generator-control/genfield/Ourtasks/GenfieldTask.h

/******************************************************************************
* File Name          : GenfieldTask.h
* Date First Issued  : 01/06/2020
* Description        : Genfield function w STM32CubeMX w FreeRTOS
*******************************************************************************/

#ifndef __GENFIELDTASK
#define __GENFIELDTASK

#include <stdint.h>
#include "FreeRTOS.h"
#include "task.h"
#include "cmsis_os.h"
#include "stm32f1xx_hal.h"
#include "adc_idx_v_struct.h"
#include "CanTask.h"

/* 
=========================================      
CAN msgs: 
ID suffix: "_i" = incoming msg; "_r" response msg

RECEIVED msgs directed into genfield function:
 (1) genfield command (also keep-alive) "cid_keepalive_i"
     payload[0]
       bit 7 - connect request
       bit 6 - reset critical error
 (2) poll (time sync) "cid_gps_sync"
 (3) function command (diagnostic poll) "cid_cmd_i"
    
SENT by genfield function:
 (1) genfield command "cid_keepalive_r" (response to "cid_keepalive_i")
     payload[0]
       bit 7 - faulted (code in payload[2])
       bit 6 - warning: minimum pre-chg immediate connect.
              (warning bit only resets with power cycle)
		 bit[0]-[3]: Current main state code

     payload[1] = critical error state error code
         0 = No fault
         1 = battery string voltage (hv1) too low
         2 = genfield 1 de-energized, aux1 closed
         3 = genfield 2 de-energized, aux2 closed
         4 = genfield #1 energized, after closure delay aux1 open
         5 = genfield #2 energized, after closure delay aux2 open
         6 = genfield #1 does not appear closed
         7 = Timeout before pre-charge voltage reached cutoff
         8 = Genfield #1 closed but voltage across it too big
         9 = Genfield #2 closed but voltage across it too big

		payload[2]
         bit[0]-[3] - current substate CONNECTING code
         bit[4]-[7] - current substate (spare) code

 poll  (response to "cid_gps_sync") & heartbeat
 (2)  "cid_msg1" hv #1 : current #1  battery string voltage:current
 (3)	"cid_msg2" hv #2 : hv #3       DMOC+:DMOC- voltages

 function command "cid_cmd_r"(response to "cid_cmd_i")
 (4)  conditional on payload[0], for example(!)--
      - ADC ct for calibration purposes hv1
      - ADC ct for calibration purposes hv2
      - ADC ct for calibration purposes hv3
      - ADC ct for calibration purposes current1
      - ADC ct for calibration purposes current2
      - Duration: (Energize coil 1 - aux 1)
      - Duration: (Energize coil 2 - aux 2)
      - Duration: (Drop coil 1 - aux 1)
      - Duration: (Drop coil 2 - aux 2)
      - volts: 12v CAN supply
      - volts: 5v regulated supply
      ... (many and sundry)

 heartbeat (sent in absence of keep-alive msgs)
 (5)  "cid_hb1" Same as (2) above
 (6)  "cid_hb2" Same as (3) above

=========================================    
NOTES:
1. GENFIELD DESIGNATION--
   (Important for following GenfieldStates.c code)

   a. Two genfield configuration
      #1 Battery string plus-to-DMOC plus
      #2 Battery string minus-to-DMOC minus
          with pre-charge resistor across #2's contacts.

   b. One genfield (with small pre-charge relay)
      #1 Battery string plus-to-DMOC plus
      #2 Battery string plus-to-pre-charge resistor,
          with pre-charge resistor to DMOC plus

2. The command/keep-alive msgs are sent
   - As a response to every command/keep-alive
   - Immediately when the program state changes
   - Every keep-alive timer timeout when incoming keep-alive
     msgs are not being receive, i.e. becomes a status heartbeat.

3. hv3 cannot measure negative voltages which might occur during
   regeneration with genfield #2 closed.  Likewise, hv2 can 
   exceed hv1 so that the difference becomes negative.  In both
   case the negative values would be small.

*/


/* Task notification bit assignments. */
#define CNCTBIT00	(1 << 0)  // ADCTask has new readings
#define CNCTBIT01	(1 << 1)  // HV sensors usart RX line ready
#define CNCTBIT02	(1 << 2)  // spare
#define CNCTBIT03	(1 << 3)  // TIMER 3: uart RX keep-alive
#define CNCTBIT04	(1 << 4)  // TIMER 1: Command Keep Alive
#define CNCTBIT05	(1 << 5)  // TIMER 2: Multiple use delays
// MailboxTask notification bits for CAN msg mailboxes
#define CNCTBIT06	(1 << 6)  // CANID_CMD: incoming command:        cid_cmd_i 
#define CNCTBIT07	(1 << 7)  // CANID-keepalive connect command:    cid_keepalive_i
#define CNCTBIT08	(1 << 8)  // CANID-GPS time sync msg (poll msg): cid_gps_sync

/* Event status bit assignments (CoNtaCTor EVent ....) */
#define CNCTEVTIMER1 (1 << 0) // 1 = timer1 timed out: command/keep-alive
#define CNCTEVTIMER2 (1 << 1) // 1 = timer2 timed out: delay
#define CNCTEVTIMER3 (1 << 2) // 1 = timer3 timed out: uart RX/keep-alive
#define CNCTEVCACMD  (1 << 3) // 1 = CAN rcv: general purpose command
#define CNCTEVCANKA  (1 << 4) // 1 = CAN rcv: Keep-alive/command
#define CNCTEVCAPOL  (1 << 5) // 1 = CAN rcv: Poll
#define CNCTEVCMDRS  (1 << 6) // 1 = Command to reset
#define CNCTEVCMDCN  (1 << 7) // 1 = Command to connect
#define CNCTEVHV     (1 << 8) // 1 = New HV readings
#define CNCTEVADC    (1 << 9) // 1 = New ADC readings

/* Output status bit assignments */
#define CNCTOUT00K1  (1 << 0) // 1 = genfield #1 energized
#define CNCTOUT01K2  (1 << 1) // 1 = genfield #2 energized
#define CNCTOUT02X1  (1 << 2) // 1 = aux #1 closed
#define CNCTOUT03X2  (1 << 3) // 1 = aux #2 closed
#define CNCTOUT04EN  (1 << 4) // 1 = DMOC enable FET
#define CNCTOUT05KA  (1 << 5) // 1 = CAN msg queue: KA status
#define CNCTOUT06KAw (1 << 6) // 1 = genfield #1 energized & pwm'ed
#define CNCTOUT07KAw (1 << 7) // 1 = genfield #2 energized & pwm'ed
#define CNCTOUTUART3 (1 << 8) // 1 = uart3 rx with high voltage timer timed out

/* AUX contact pins. */
#define AUX1_GPIO_REG GPIOA
#define AUX1_GPIO_IN  GPIO_PIN_1
#define AUX2_GPIO_REG GPIOA
#define AUX2_GPIO_IN  GPIO_PIN_5

/* HV by-pass jumper pin. */
#define HVBYPASSPINPORT GPIOA
#define HVBYPASSPINPIN  GPIO_PIN_3

/* Command request bits assignments. */
#define CMDCONNECT (1 << 7) // 1 = Connect requested; 0 = Disconnect requested
#define CMDRESET   (1 << 6) // 1 = Reset fault requested; 0 = no command

/* Number of different CAN id msgs this function sends. */
# define NUMCANMSGS 6

/* High voltage readings */
//#define HVSCALEbits 16  // Scale factor HV

struct CNCNTHV
{
	struct IIRFILTERL iir; // Intermediate filter params
//   double dhv;            // Calibrated
	double dscale;         // volts/tick
	double dhvc;           // HV calibrated
	uint32_t hvcal;        // Calibrated, scaled volts/adc tick
	uint32_t hvc;          // HV as scaled volts
	uint16_t hv;           // Raw ADC reading as received from uart

};

/* Fault codes */
enum GENFIELD_FAULTCODE
{
	NOFAULT,
	BATTERYLOW,
	GENFIELD1_OFF_AUX1_ON,
	GENFIELD2_OFF_AUX2_ON,
	GENFIELD1_ON_AUX1_OFF,
	GENFIELD2_ON_AUX2_OFF,
	GENFIELD1_DOES_NOT_APPEAR_CLOSED,
   PRECHGVOLT_NOTREACHED,
	GENFIELD1_CLOSED_VOLTSTOOBIG,
	GENFIELD2_CLOSED_VOLTSTOOBIG,
	KEEP_ALIVE_TIMER_TIMEOUT,
	NO_UART3_HV_READINGS,
	HE_AUTO_ZERO_TOLERANCE_ERR,
};

enum GENFIELD_STATE
{
	DISCONNECTED,   /*  0 */
	CONNECTING,     /*  1 */
	CONNECTED,      /*  2 */
	FAULTING,       /*  3 */
	FAULTED,        /*  4 */
	RESETTING,      /*  5 */
	DISCONNECTING,  /*  6 */
	OTOSETTLING,    /*  7 one time intializing. */
};

/* Function command response payload codes. */
enum GENFIELD_CMD_CODES
{
	ADCRAW5V,         // PA0 IN0  - 5V sensor supply
	ADCRAWCUR1,       // PA5 IN5  - Current sensor: total battery current
	ADCRAWCUR2,       // PA6 IN6  - Current sensor: motor
	ADCRAW12V,        // PA7 IN7  - +12 Raw power to board
	ADCINTERNALTEMP,  // IN17     - Internal temperature sensor
	ADCINTERNALVREF,  // IN18     - Internal voltage reference
	UARTWHV1,
	UARTWHV2,
	UARTWHV3,
	CAL5V,
	CAL12V,
};

/* CAN msg array index names. */
enum CANCMD_R
{
CID_KA_R,
CID_MSG1,
CID_MSG2,
CID_CMD_R,
CID_HB1,
CID_HB2,
};

/* Working struct for Genfield function/task. */
// Prefixes: i = scaled integer, f = float
// Suffixes: k = timer ticks, t = milliseconds
struct GENFIELDFUNCTION
{
   // Parameter loaded either by high-flash copy, or hard-coded subroutine
	struct GENFIELDLC lc; // Parameters for genfields, (lc = Local Copy)

	struct ADCFUNCTION* padc; // Pointer to ADC working struct

	/* Events status */
	uint32_t evstat;

	/* Output status */
	uint32_t outstat;
	uint32_t outstat_prev;

	/* Current fault code */
	enum GENFIELD_FAULTCODE faultcode;
	enum GENFIELD_FAULTCODE faultcode_prev;

	/* OTO settling */
	uint32_t otosw;

/* In the disconnect state the battery string voltage must be above the following. */
	uint32_t ibattlow;   // Minimum battery volts required to connect

/* Battery string current above which disconnecting is prevented. */
	int32_t icurrentdisconnect; // Scale integer representation

/* With two genfield config, (hv1-hv2) max when genfield #1 closes */
/* In one genfield config, (hv1-hv2) max when genfield #2 closes */
	uint32_t ihv1mhv2max;

	uint32_t iprechgendv;  // Prep-charge end volts threshold: two genfield mode
	uint32_t iprechgendvb; // Prep-charge end volts threshold: one genfield mode (b)


/* Mininum pre-charge delay (before monitoring voltage) */
   uint32_t prechgmin_k; // Minimum pre-charge duration

	uint32_t idiffafter; //  Scaled int of lc.diffafter

	uint32_t ka_k;       // Command/Keep-alive CAN msg timeout duration.
	uint32_t prechgmax_k;// allowable delay for diffafter to reach closure point (timeout delay ticks)
	uint32_t close1_k;   // genfield #1 coil energize-closure (timeout delay ticks)
	uint32_t close2_k;   // genfield #2 coil energize-closure (timeout delay ticks)
	uint32_t open1_k;    // genfield #1 coil de-energize-open (timeout delay ticks)
	uint32_t open2_k;    // genfield #2 coil de-energize-open (timeout delay ticks)
	uint32_t keepalive_k;// keep-alive timeout (timeout delay ticks)
	uint32_t hbct1_k;		// Heartbeat ct: ticks between sending msgs hv1:cur1
	uint32_t hbct2_k;		// Heartbeat ct: ticks between sending msgs hv2:cur2

	uint32_t ihv1;       // Latest reading: battery string at genfield #1
	uint32_t ihv2;       // Latest reading: DMOC side of genfield #1
	uint32_t ihv3;       // Latest reading: Pre-charge R, (if two genfield config)
	int32_t hv1mhv2;     // Voltage across genfield #1 from latest readings

	uint32_t statusbits;
	uint32_t statusbits_prev;

	/* Setup serial receive for uart (HV sensing) */
	struct SERIALRCVBCB* prbcb3;	// usart3

	TimerHandle_t swtimer1; // Software timer1: command/keep-alive
	TimerHandle_t swtimer2; // Software timer2: multiple purpose delay
	TimerHandle_t swtimer3; // Software timer3: uart RX/keep-alive

	/* High voltage readings */
	struct CNCNTHV hv[NUMHV];
	uint32_t hvuartctr;	// Running count of uart lines received from hv sensor

	/* Pointers to incoming CAN msg mailboxes. */
	struct MAILBOXCAN* pmbx_cid_cmd_i;      //
	struct MAILBOXCAN* pmbx_cid_keepalive_i; //
	struct MAILBOXCAN* pmbx_cid_gps_sync;   //

	uint32_t ipwmpct1;     // Period ct PWM after closure delay at 100% coil #1
	uint32_t ipwmpct2;     // Period ct PWM after closure delay at 100% coil #2

	/* PWM struct */
	TIM_OC_InitTypeDef sConfigOCn; // 'n' - serves ch3 and ch4
	
	uint8_t state;      // Genfield main state
	uint8_t substateC;  // State within CONNECTING (0-15)
	uint8_t substateX;  // spare substate (0-15)

	/* CAN msgs */
	struct CANTXQMSG canmsg[NUMCANMSGS];
};

/* *************************************************************************/
osThreadId xGenfieldTaskCreate(uint32_t taskpriority);
/* @brief	: Create task; task handle created is global for all to enjoy!
 * @param	: taskpriority = Task priority (just as it says!)
 * @return	: GenfieldTaskHandle
 * *************************************************************************/
void StartGenfieldTask(void const * argument);
/*	@brief	: Task startup
 * *************************************************************************/

extern struct GENFIELDFUNCTION genfieldfunction;
extern osThreadId GenfieldTaskHandle;

#endif
