generator-control/genfield/Ourtasks/genfield_idx_v_struct.h

/******************************************************************************
* File Name          : genfield_idx_v_struct.h
* Date First Issued  : 06/26/2019
* Board              :
* Description        : Load parameter struct
*******************************************************************************/

#include <stdint.h>
#include "common_can.h"
#include "iir_filter_lx.h"
#include "GenfieldTask.h"

#ifndef __GENFIELD_IDX_V_STRUCT
#define __GENFIELD_IDX_V_STRUCT

/* Hardware configuration option bit assignments. */
#define AUX1PRESENT   (1 << 0)  // 1 = Genfield #1 has auxilary contacts
#define AUX1SENSE     (1 << 1)  // 1 = Aux I/O bit with Genfield #1 closed
#define AUX2PRESENT   (1 << 2)  // 1 = Genfield #2 has auxilary contacts
#define AUX2SENSE     (1 << 3)  // 1 = Aux I/O bit with Genfield #2 closed
#define ONEGENFIELD  (1 << 4)  // 1 = One genfield; one small pre-charge relay
#define PWMGENFIELD1 (1 << 5)  // 1 = PWM'ing is used on coil #1
#define PWMGENFIELD2 (1 << 6)  // 1 = PWM'ing is used on coil #2
#define PWMNOHVSENSOR (1 << 7)  // 1 = No high voltage sensor, (ignore hv readings)

/* High Voltage readings arrive in on uart line. */
#define NUMHV 3       // Number of hv readings
#define	IDXHV1  0 // High voltage reading: battery string side of genfield
#define	IDXHV2  1 // High voltage reading: DMOC+ side of genfield
#define	IDXHV3  2 // High voltage reading: across pre-charge resistor (two genfields)

#define HVSCALE (1 << 17) // High voltage integer scaling for hvcal


/* Calibration parameter, float */
// Use double for F103 to save float->double conversions
struct CNTCTCALHV
{
	struct IIR_L_PARAM iir; // Filter: Time constant, integer scaling
	double dvcal;       // Calibration voltage applied
	uint32_t adchv;     // ADC reading for calibration voltage
	uint32_t offset;    // ADC reading for Sensor zero
};
struct CNTCTCALF
{
	double offset;
	double scale;
};
/* Calibration parameters, scaled integer */
struct CNTCTCALSI
{
	int32_t offset;
	int32_t scale;
};

/* Parameters genfield instance */
struct GENFIELDLC
 {
	uint32_t size;			// Number of items in struct
 	uint32_t crc;			// crc-32 placed by loader
	uint32_t version;		// struct version number
	double ddiffb4;      // hv1-hv2 voltage difference before closing (volts)

/* NOTE: 
   - all suffix _t parameters are times in milliseconds
   - all voltages are in volts; prefix 'f' designates float */
	
/* Hardware configuration option bits. */
   uint32_t hwconfig;

/* Command/Keep-alive CAN msg timeout duration. */
	uint32_t ka_t;       // (e.g. 1000 ms)

/* uart RX keep-alive timeout duration. */
   uint32_t ksRX_t;     // (e.g. 10 ms)

/* In the disconnect state the battery string voltage must be above the following. */
	float fbattlow;      // Minimum battery volts required to connect

/* Battery string current above which disconnecting is prevented. */
	double dcurrentdisconnect;   // Parameter specification made in fp

/* Genfield #1 closure time delay */
	uint32_t close1_t;   // Delay: genfield #1 coil energize->closed

/* Genfield #2, or pre-charge relay, closure time delay */
	uint32_t close2_t;   // Delay: #2 coil energize->closed
   
/* Genfield #1 open time delay */
	uint32_t open1_t;   // Delay: genfield #1 coil de-energize->open

/* Genfield #2, or pre-charge relay, open time delay */
	uint32_t open2_t;   // Delay: #2 coil de-energize->open

/* Mininum pre-charge delay (before monitoring voltage) */
   uint32_t prechgmin_t; // Minimum pre-charge duration

/* Maximum pre-charge wait, after prechgmin_t, for voltage threshold
   to be reached. */
   uint32_t prechgmax_t; // Maximum allowed for voltage to reach threshold

/* Allowable hv1-hv2 voltage difference after closure (volts) */
	float fdiffafter;

/* HV2 reading stable after closure (duration ms) */
	uint32_t hv2stable_t;

/* PWM durations (0.0- 100.0) */
   float  fpwmpct1;     // Percent PWM after closure delay at 100% coil #1
   float  fpwmpct2;     // Percent PWM after closure delay at 100% coil #2

/* Message timings. */
	uint32_t keepalive_t;// keep-alive timeout (timeout delay ms)
	uint32_t hbct1_t;		// Heartbeat ct: ticks between sending msgs hv1:cur1
	uint32_t hbct2_t;		// Heartbeat ct: ticks between sending msgs hv2:cur2
	uint32_t hbct3_t;		// Heartbeat ct: ticks between sending msgs hv3 (if two genfields)

/* Calibrations (offset, scale) */

	// High voltage from uart
	struct CNTCTCALHV calhv[NUMHV]; 

/* Send CAN ids  */
	uint32_t cid_hb1;    // CANID-Heartbeat msg volt1:cur1 (volts:amps)
	uint32_t cid_hb2;    // CANID-Heartbeat msg volt2:cur2 (volts:amps)
   uint32_t cid_msg1;   // CANID-genfield poll response msg: volt1:cur1 (volts:amps)
   uint32_t cid_msg2;   // CANID-genfield poll response msg: volt2:cur2 (volts:amps)
	uint32_t cid_cmd_r;  // CANID_CMD_CNTCTR1R
	uint32_t cid_keepalive_r; // CANID-keepalive response (status)

/* Receive CAN ids List of CAN ID's for setting up hw filter */
	uint32_t cid_cmd_i;       // CANID_CMD: incoming command
	uint32_t cid_keepalive_i;// CANID-keepalive connect command
	uint32_t cid_gps_sync;    // CANID-GPS time sync msg (poll msg)
	uint32_t code_CAN_filt[5];// Spare
 };

/* *************************************************************************/
void genfield_idx_v_struct_hardcode_params(struct GENFIELDLC* p);
/* @brief	: Init struct from hard-coded parameters (rather than database params in highflash)
 * @return	: 0
 * *************************************************************************/
 
#endif
