generator-control/genfield/Ourwares/ADCTask.c

/******************************************************************************
* File Name          : ADCTask.c
* Date First Issued  : 02/01/2019
* Description        : Processing ADC readings after ADC/DMA issues interrupt
*******************************************************************************/

#include "FreeRTOS.h"
#include "task.h"
#include "cmsis_os.h"
#include "malloc.h"

#include "ADCTask.h"
#include "adctask.h"
#include "morse.h"
#include "adcfastsum16.h"
#include "adcparams.h"
#include "GenfieldTask.h"
#include "adcextendsum.h"

void StartADCTask(void const * argument);

uint32_t adcsumdb[6]; // debug
uint32_t adcdbctr = 0;// debug

osThreadId ADCTaskHandle;

extern ADC_HandleTypeDef hadc1;

extern osThreadId GenfieldTaskHandle;

/* *************************************************************************
 * osThreadId xADCTaskCreate(uint32_t taskpriority);
 * @brief	: Create task; task handle created is global for all to enjoy!
 * @param	: taskpriority = Task priority (just as it says!)
 * @return	: ADCTaskHandle
 * *************************************************************************/
osThreadId xADCTaskCreate(uint32_t taskpriority)
{
 	osThreadDef(ADCTask, StartADCTask, osPriorityNormal, 0, 128);
	ADCTaskHandle = osThreadCreate(osThread(ADCTask), NULL);
	vTaskPrioritySet( ADCTaskHandle, taskpriority );
	return ADCTaskHandle;

}
/* *************************************************************************
 * void StartADCTask(void const * argument);
 *	@brief	: Task startup
 * *************************************************************************/
void StartADCTask(void const * argument)
{
	#define TSK02BIT02	(1 << 0)  // Task notification bit for ADC dma 1st 1/2 (adctask.c)
	#define TSK02BIT03	(1 << 1)  // Task notification bit for ADC dma end (adctask.c)

	uint16_t* pdma;

	/* A notification copies the internal notification word to this. */
	uint32_t noteval = 0;    // Receives notification word upon an API notify

	/* notification bits processed after a 'Wait. */
	uint32_t noteused = 0;

	/* Get buffers, "our" control block, and ==>START<== ADC/DMA running. */
	struct ADCDMATSKBLK* pblk = adctask_init(&hadc1,TSK02BIT02,TSK02BIT03,&noteval);
	if (pblk == NULL) {morse_trap(15);}

  /* Infinite loop */
  for(;;)
  {
		/* Wait for DMA interrupt notification from adctask.c */
		xTaskNotifyWait(noteused, 0, &noteval, portMAX_DELAY);
		noteused = 0;	// Accumulate bits in 'noteval' processed.

		/* We handled one, or both, noteval bits */
		noteused |= (pblk->notebit1 | pblk->notebit2);

		if (noteval & TSK02BIT02)
		{
			pdma = adc1dmatskblk[0].pdma1; // [0] = adc1
		}
		else
		{
			pdma = adc1dmatskblk[0].pdma2;
		}

		/* Sum the readings 1/2 of DMA buffer to an array. */
		adcfastsum16(&adc1.chan[0], pdma); // Fast in-line addition
		adc1.ctr += 1; // Update count

#define DEBUGGINGADCREADINGS
#ifdef DEBUGGINGADCREADINGS
		/* Save sum for defaultTask printout for debugging */
		adcsumdb[0] = adc1.chan[0].sum;
		adcsumdb[1] = adc1.chan[1].sum;
		adcsumdb[2] = adc1.chan[2].sum;
		adcsumdb[3] = adc1.chan[3].sum;
		adcsumdb[4] = adc1.chan[4].sum;
		adcsumdb[5] = adc1.chan[5].sum;
		adcdbctr += 1;
#endif

		/* Extended sum for smoothing and display. */
		adcextendsum(&adc1);

		/* Calibrate and filter ADC readings. */
		adcparams_cal();

		/* Notify GenfieldTask that new readings are ready. */
		if( GenfieldTaskHandle == NULL) morse_trap(51); // JIC task has not been created
		
		xTaskNotify(GenfieldTaskHandle, CNCTBIT00, eSetBits);
  }
}
