generator-control/genfield/Ourwares/CanTask.c

/******************************************************************************
* File Name          : CanTask.c
* Date First Issued  : 01/01/2019
* Description        : CAN interface to FreeRTOS/ST HAL
*******************************************************************************/

#include "stm32f1xx_hal.h"
#include "stm32f1xx_hal_can.h"
#include "CanTask.h"
#include "can_iface.h"
#include "morse.h"

void StartCanTxTask(void const * argument);
void StartCanRxTask(void const * argument);

osThreadId CanTxTaskHandle;
QueueHandle_t CanTxQHandle;

/* ====== Tx ==============================================================*/
/* *************************************************************************
 * void canmsg_expand(CAN_TxHeaderTypeDef *phal, uint8_t *pdat, struct CANRCVBUF *pcan);
 * @brief	: Convert hardware compressed format to silly HAL expanded format
 * @param	: phal = pointer to HAL output
 * @param	: pdat = pointer to HAL payload data array
 * @param	: pcan = pointer to convenient hardware format
 * *************************************************************************/
void canmsg_expand(CAN_TxHeaderTypeDef *phal, uint8_t *pdat, struct CANRCVBUF *pcan)
{
	phal->StdId = (pcan->id >> 21);
	phal->ExtId = (pcan->id >>  3);
	phal->IDE   = (pcan->id & CAN_ID_EXT);
	phal->RTR   = (pcan->id & CAN_RTR_REMOTE);
	phal->DLC   = (pcan->dlc & 0x7);
	*(pdat+0) = pcan->cd.uc[0];
	*(pdat+1) = pcan->cd.uc[1];
	*(pdat+2) = pcan->cd.uc[2];
	*(pdat+3) = pcan->cd.uc[3];
	*(pdat+4) = pcan->cd.uc[4];
	*(pdat+5) = pcan->cd.uc[5];
	*(pdat+6) = pcan->cd.uc[6];
	*(pdat+7) = pcan->cd.uc[7];
	return;
}

/* *************************************************************************
 * QueueHandle_t  xCanTxTaskCreate(uint32_t taskpriority, int32_t queuesize);
 * @brief	: Create task; task handle created is global for all to enjoy!
 * @param	: taskpriority = Task priority (just as it says!)
 * @param	: queuesize = number of items in Tx queue
 * @return	: QueueHandle_t = queue handle
 * *************************************************************************/
QueueHandle_t  xCanTxTaskCreate(uint32_t taskpriority, int32_t queuesize)
{
 /* definition and creation of CanTask */
  osThreadDef(CanTxTask, StartCanTxTask, osPriorityNormal, 0, 128);
  CanTxTaskHandle = osThreadCreate(osThread(CanTxTask), NULL);
	vTaskPrioritySet( CanTxTaskHandle, taskpriority );

	/* FreeRTOS queue for task with data to send. */
	CanTxQHandle = xQueueCreate(queuesize, sizeof(struct CANTXQMSG));
	return CanTxQHandle;
}
/* *************************************************************************
 * void StartCanTxTask(void const * argument);
 *	@brief	: Task startup
 * *************************************************************************/
void StartCanTxTask(void const * argument)
{
   BaseType_t Qret;	// queue receive return
	struct CANTXQMSG txq;
	int ret;

//osDelay(512*4); // Debug delay

  /* Infinite RTOS Task loop */
  for(;;)
  {
HAL_GPIO_TogglePin(GPIOD, GPIO_PIN_13); // ORANGE
		Qret = xQueueReceive(CanTxQHandle,&txq,portMAX_DELAY);
		if (Qret == pdPASS) // Break loop if not empty
		{
			ret = can_driver_put(txq.pctl, &txq.can, txq.maxretryct, txq.bits);
/* ===> Trap errors
 *				: -1 = Buffer overrun (no free slots for the new msg)
 *				: -2 = Bogus CAN id rejected
 *				: -3 = control block pointer NULL */
			if (ret == -1) morse_trap(91);
			if (ret == -2) morse_trap(92);
			if (ret == -3) morse_trap(93);
		}
  }
}
/* ====== Rx ==============================================================*/
osThreadId CanRxTaskHandle;
QueueHandle_t CanRxQHandle;

/* *************************************************************************
 * QueueHandle_t xCanRxTaskCreate(uint32_t taskpriority, int32_t queuesize);
 * @brief	: Create task; task handle created is global for all to enjoy!
 * @param	: taskpriority = Task priority (just as it says!)
 * @param	: queuesize = number of RX0 + RX1 msgs
 * @return	: CanRxQHandle
 * *************************************************************************/
QueueHandle_t xCanRxTaskCreate(uint32_t taskpriority, int32_t queuesize)
{
 /* definition and creation of CanTask */
  osThreadDef(CanRxTask, StartCanRxTask, osPriorityNormal, 0, 128);
  CanRxTaskHandle = osThreadCreate(osThread(CanRxTask), NULL);
	vTaskPrioritySet( CanRxTaskHandle, taskpriority );

	/* FreeRTOS queue for task with data to send. */
	CanRxQHandle = xQueueCreate(queuesize, sizeof(struct CANRCVBUFN));

	return CanRxQHandle;
}
/* *************************************************************************
 * void StartCanRxTask(void const * argument);
 *	@brief	: Task startup
 * *************************************************************************/
void StartCanRxTask(void const * argument)
{
/* NOTE:  Since there is just one receiving task, this task is not needed.
          However, the initialization to create the queue is needed.
*/
	vTaskSuspend( NULL );

//   BaseType_t Qret;	// queue receive return
//	struct CANRCVBUFN ncan;

  /* Infinite RTOS Task loop */
  for(;;)
  {
osDelay(11000);
//$ TODO: distribute CAN msg
//$		Qret = xQueueReceive(CanRxQHandle,&ncan,portMAX_DELAY);
  }
  return;
}
